GrowthLine/GrowthLine/GrowthLine/Fritzing Files/Growthline 1_1_bb.png

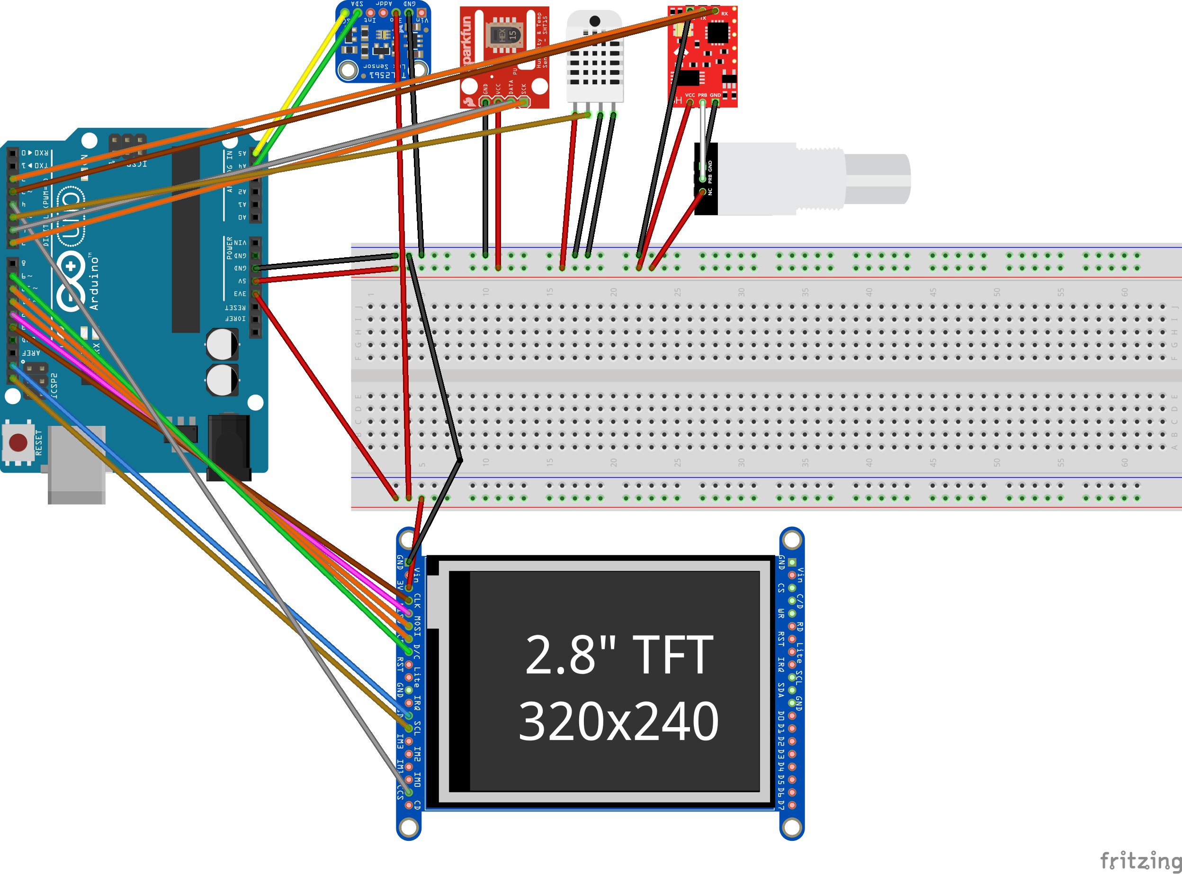
GrowthLine/Fritzing Files/Growthline 1_1_bb.png
