GrowthLine/GrowthLine/GrowthLine/Fritzing Files/Growthline 1_1_pcb.png

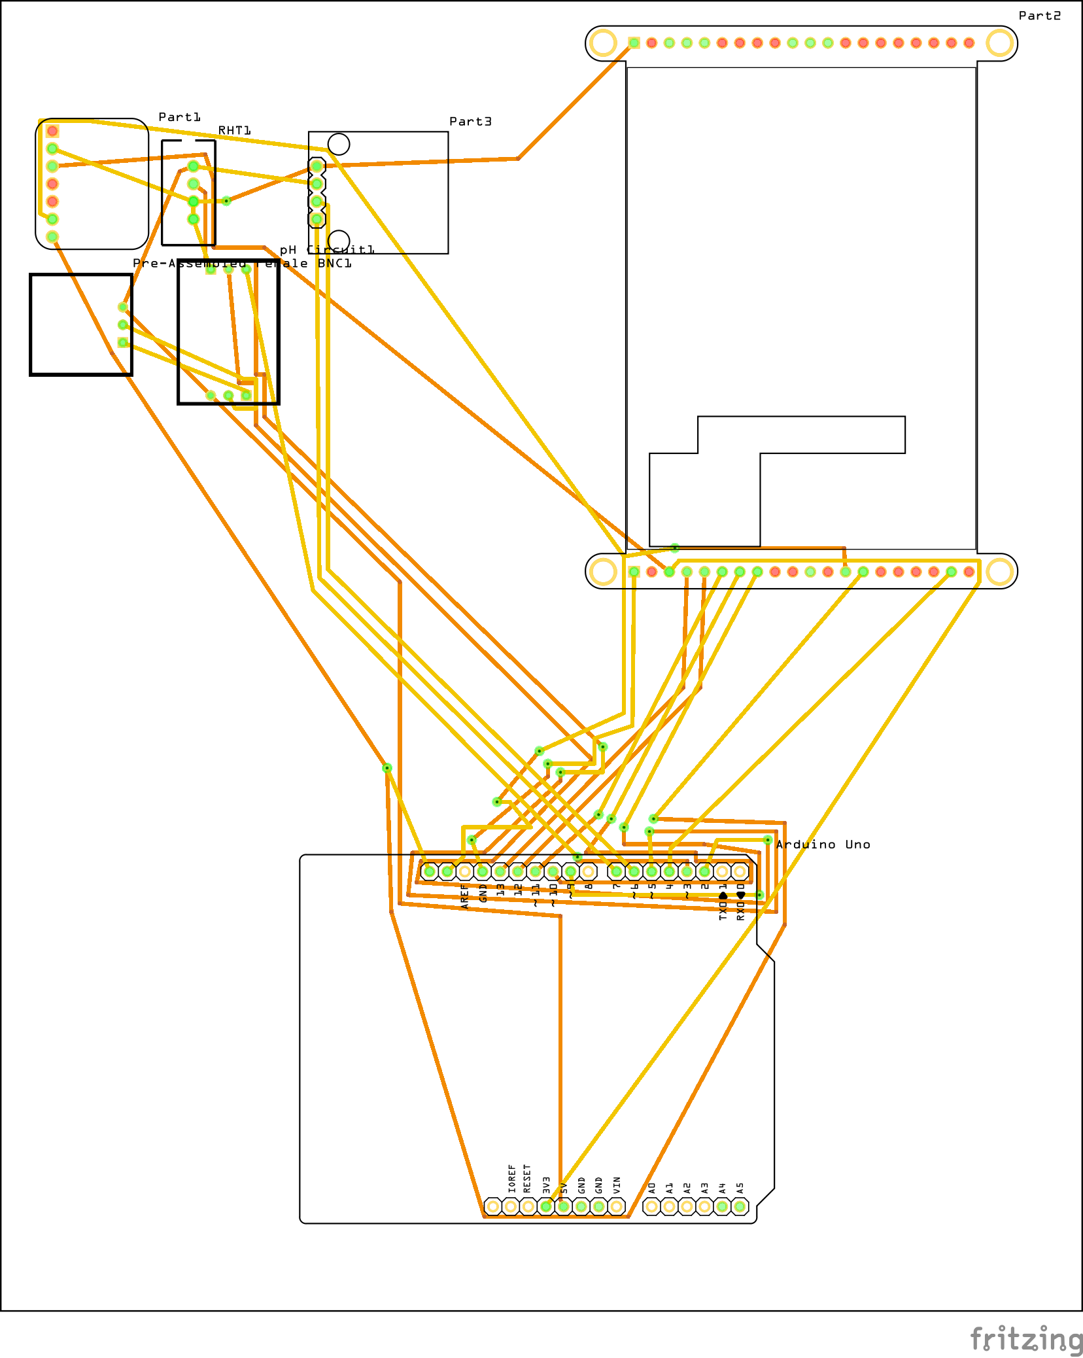
GrowthLine/Fritzing Files/Growthline 1_1_pcb.png
