GrowthLine/GrowthLine/GrowthLine/Fritzing Files/Growthline 1_1_schem.png

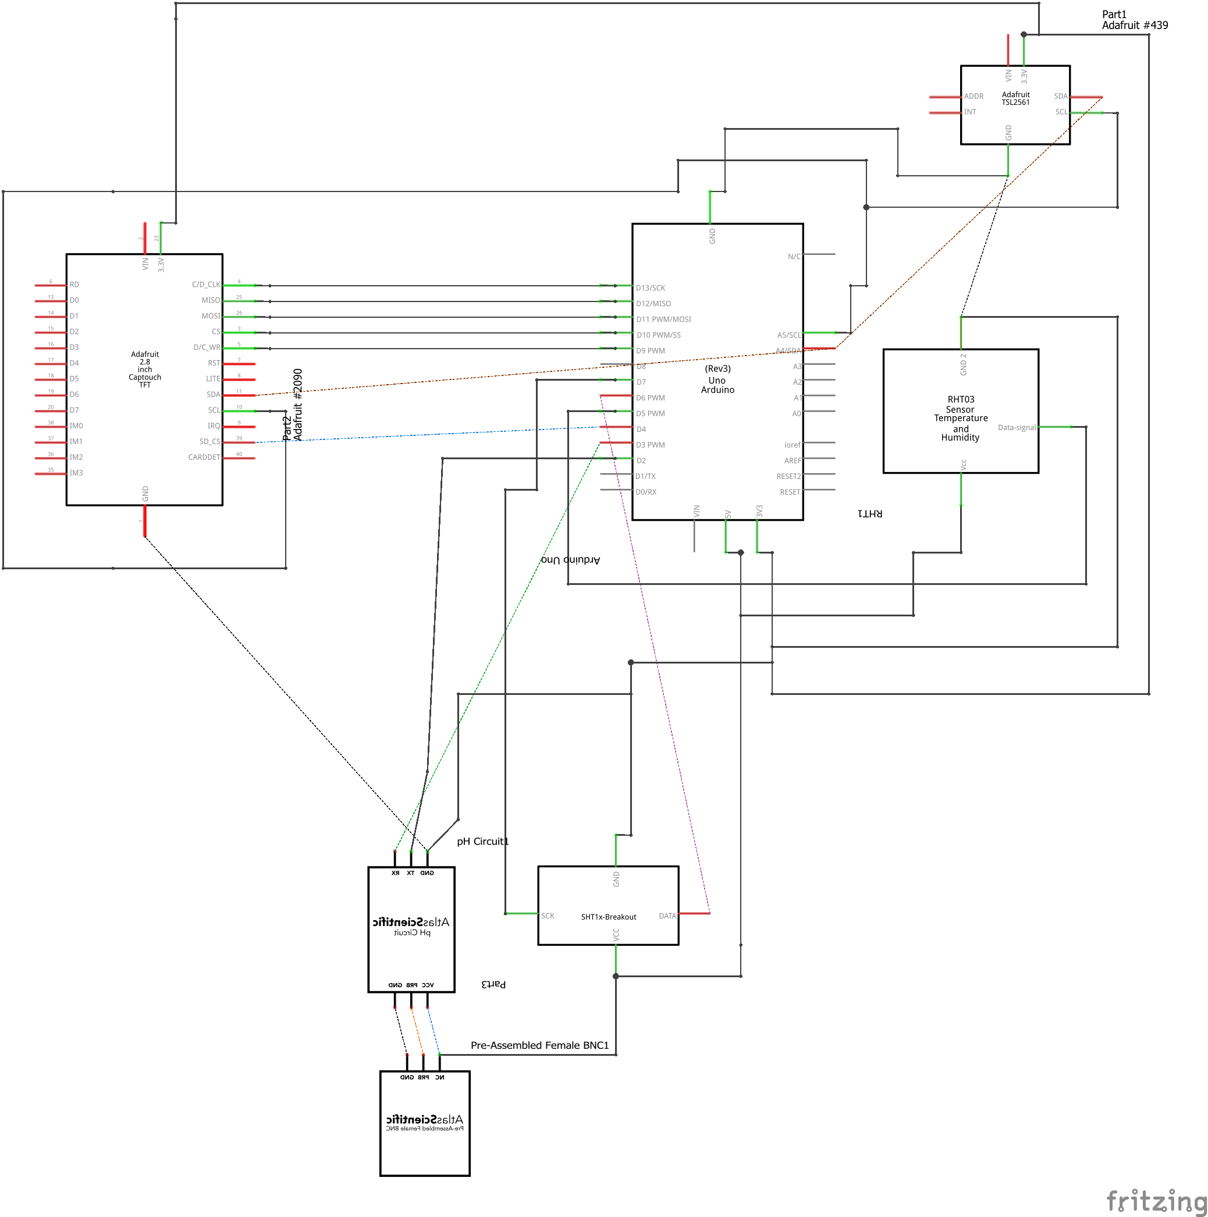
GrowthLine/Fritzing Files/Growthline 1_1_schem.png
