GrowthLine/GrowthLine/GrowthLine/Fritzing Files/Growthline labled parts.png

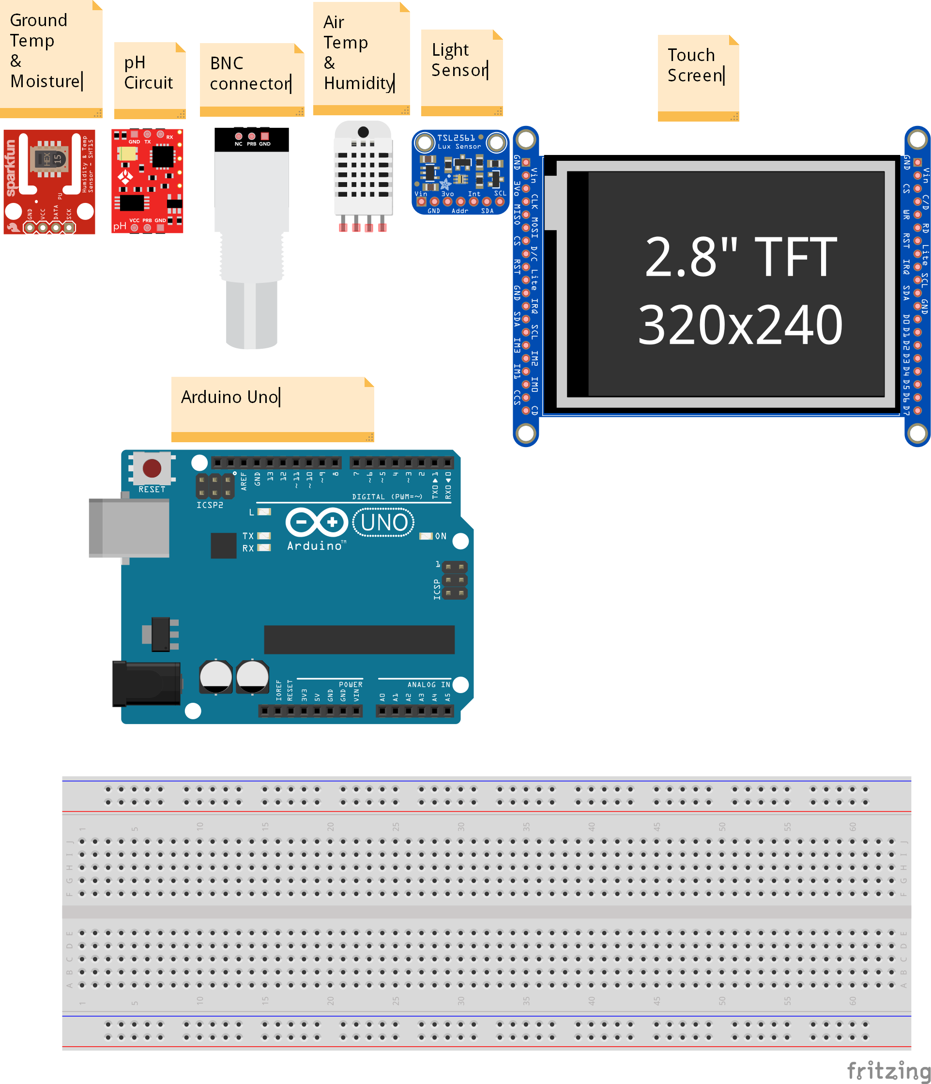
GrowthLine/Fritzing Files/Growthline labled parts.png
